klegot/ArdUno_AADsm5-42b/отчет/data/земиля земля.jpg

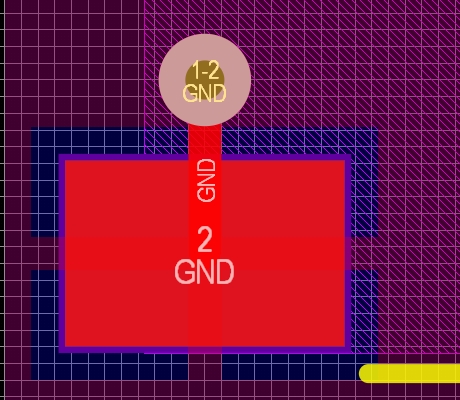
отчет/data/земиля земля.jpg
