klegot/ArdUno_AADsm5-42b/отчет/data/каталог проекта.jpg

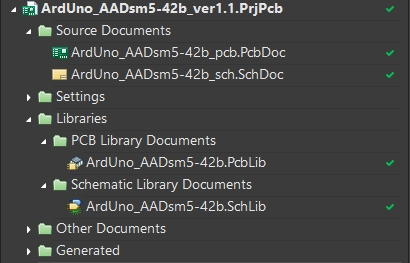
отчет/data/каталог проекта.jpg
