klegot/ArdUno_AADsm5-42b/отчет/data/3D Bottom.PNG

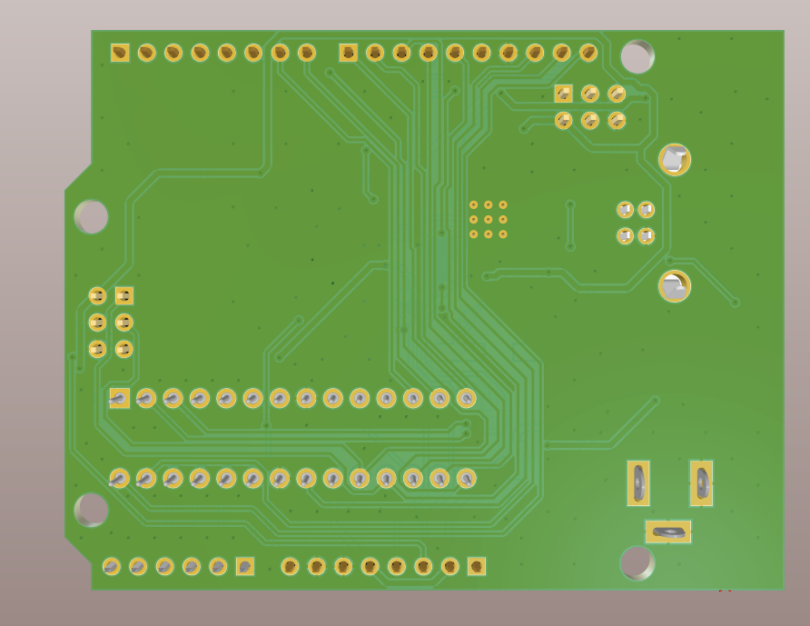
отчет/data/3D Bottom.PNG
