klegot/ArdUno_AADsm5-42b/отчет/data/3D isometric.PNG

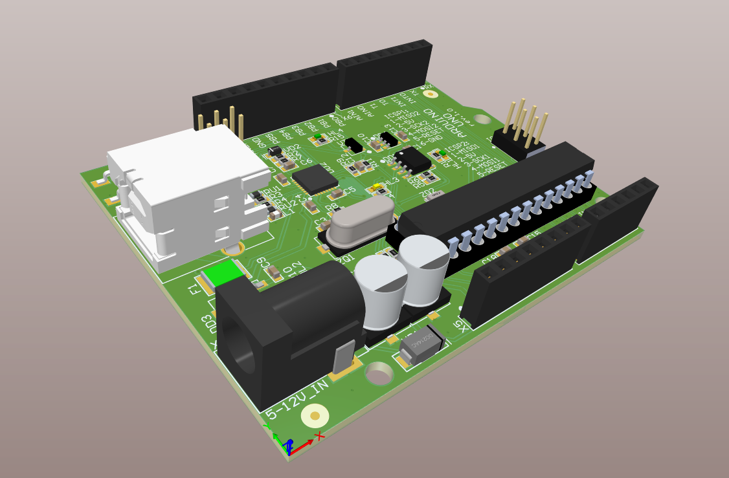
отчет/data/3D isometric.PNG
