klegot/ArdUno_AADsm5-42b/отчет/data/3D Top.PNG

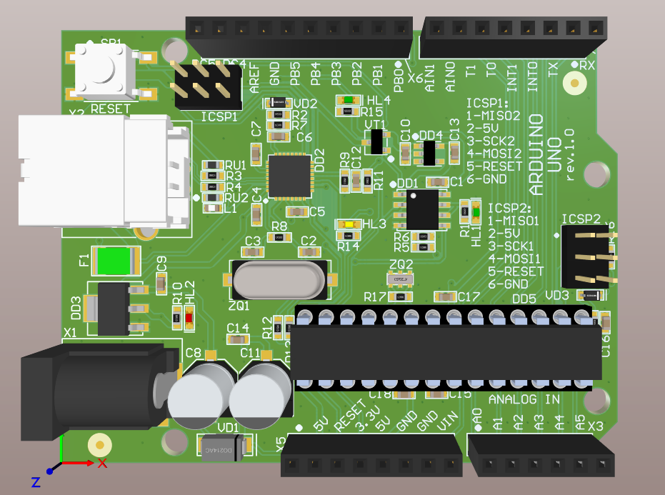
отчет/data/3D Top.PNG
