klegot/ArdUno_AADsm5-42b/отчет/data/atmega 3д.jpg

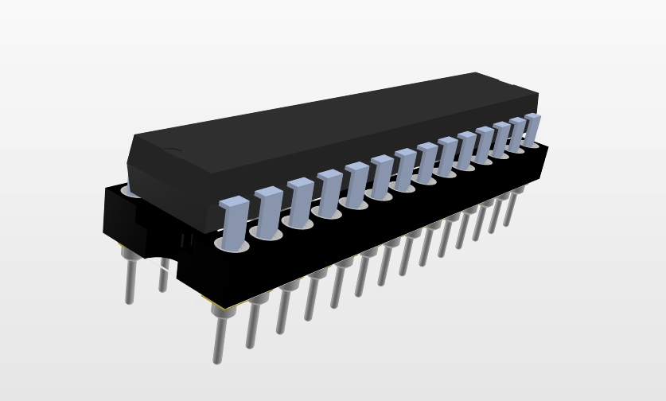
отчет/data/atmega 3д.jpg
