klegot/ArdUno_AADsm5-42b/отчет/data/atmega птм.jpg

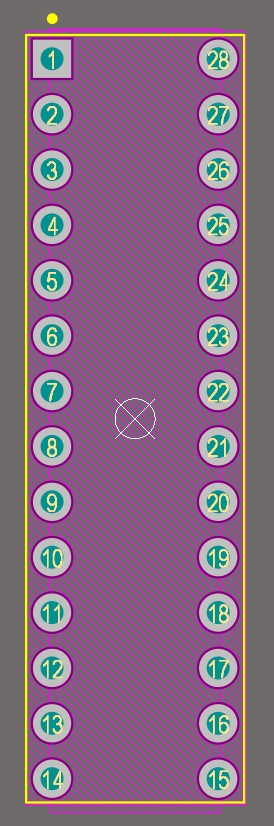
отчет/data/atmega птм.jpg
