klegot/ArdUno_AADsm5-42b/отчет/data/atmega уго + птм.jpg

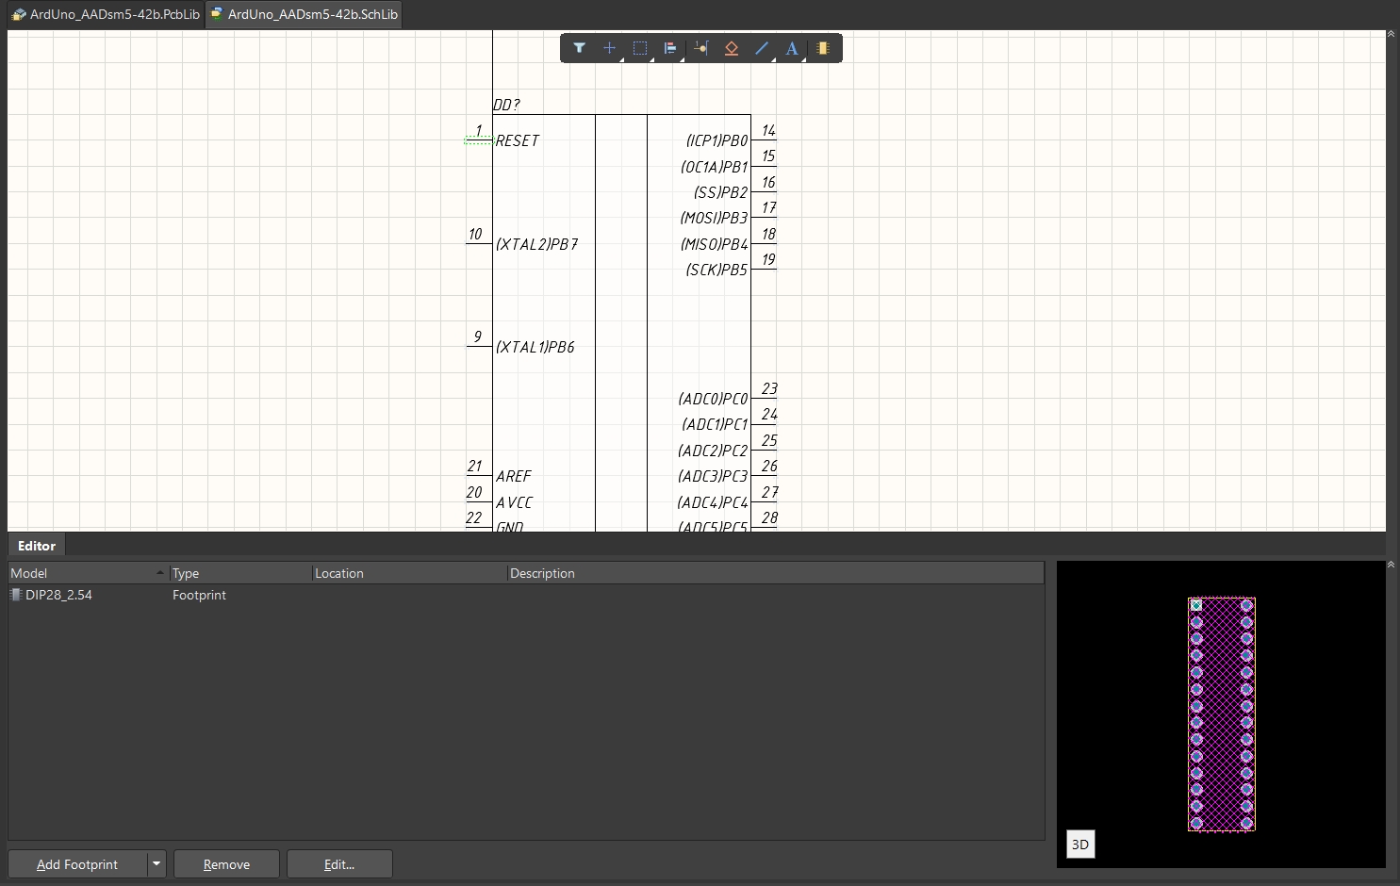
отчет/data/atmega уго + птм.jpg
