klegot/ArdUno_AADsm5-42b/отчет/data/Bottom Layer GERBER.PNG

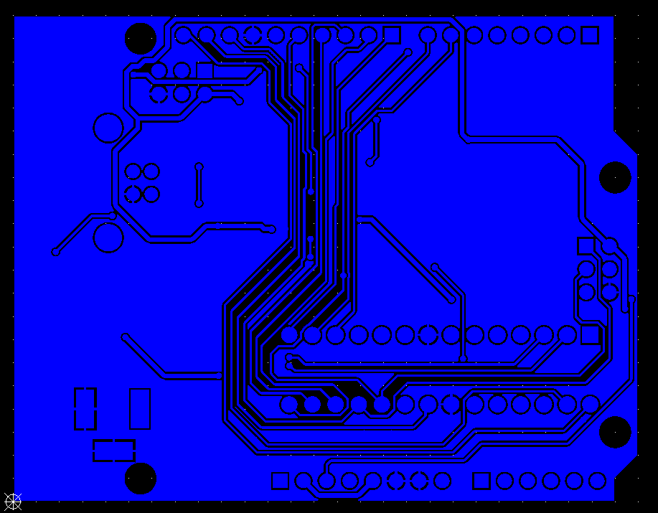
отчет/data/Bottom Layer GERBER.PNG
