klegot/ArdUno_AADsm5-42b/отчет/data/Bottom Layer.PNG

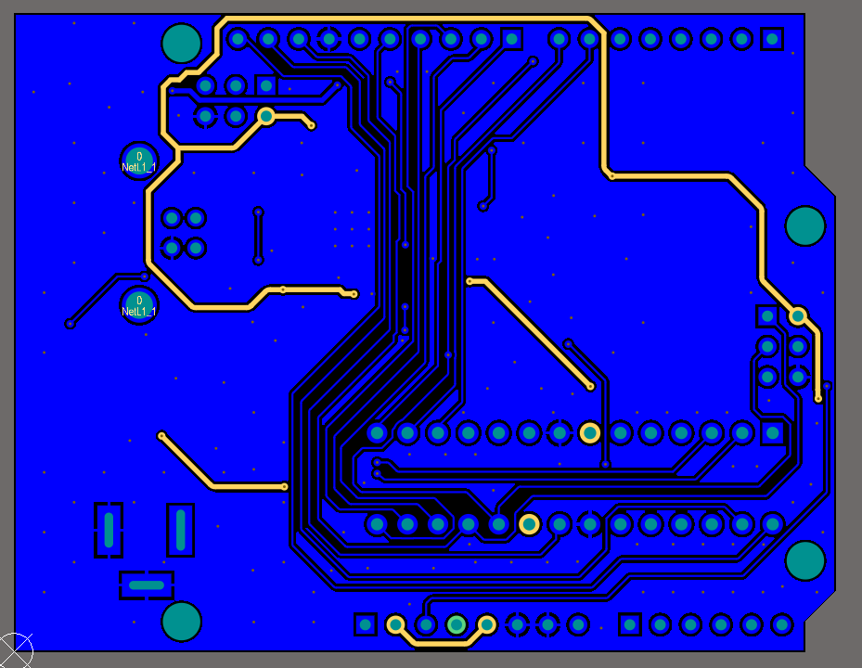
отчет/data/Bottom Layer.PNG
