klegot/ArdUno_AADsm5-42b/отчет/data/Keep Out Layer GERBER.PNG

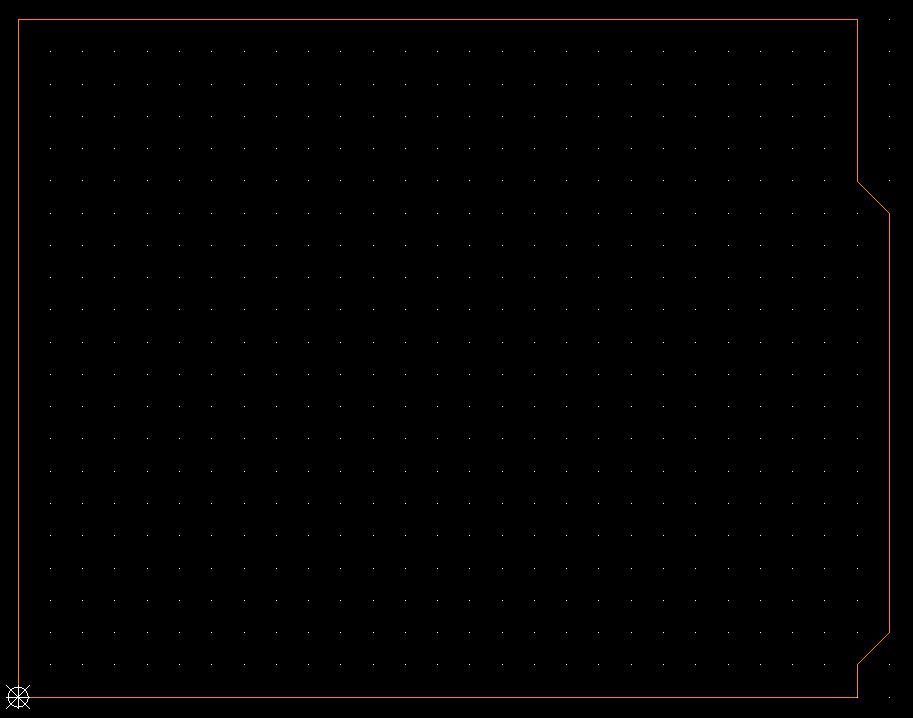
отчет/data/Keep Out Layer GERBER.PNG
