klegot/ArdUno_AADsm5-42b/отчет/data/Overlay GERBER.PNG

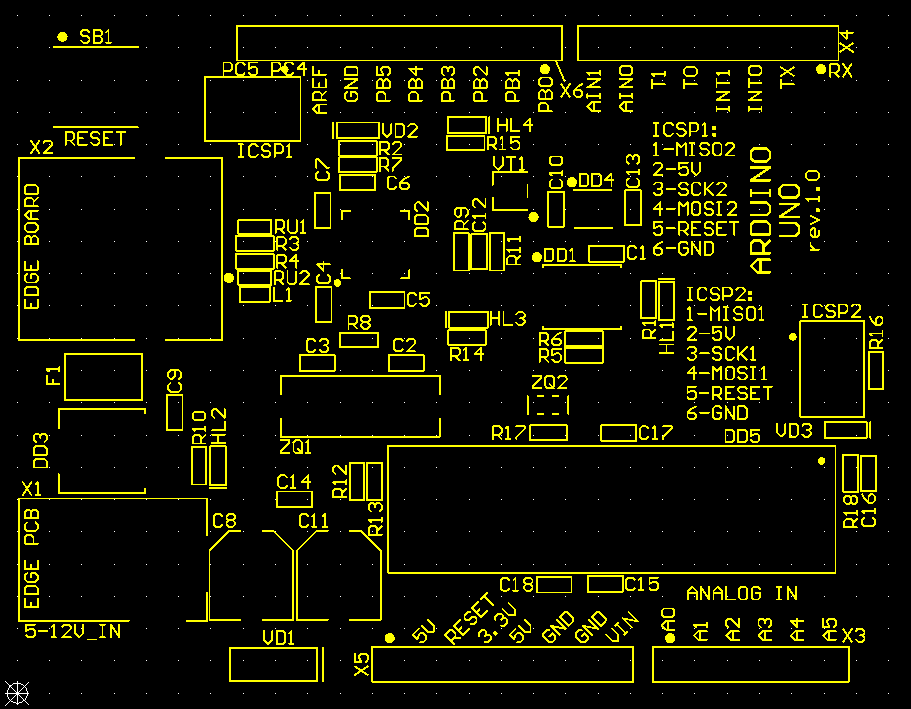
отчет/data/Overlay GERBER.PNG
