klegot/ArdUno_AADsm5-42b/отчет/data/Top Layer GERBER.PNG

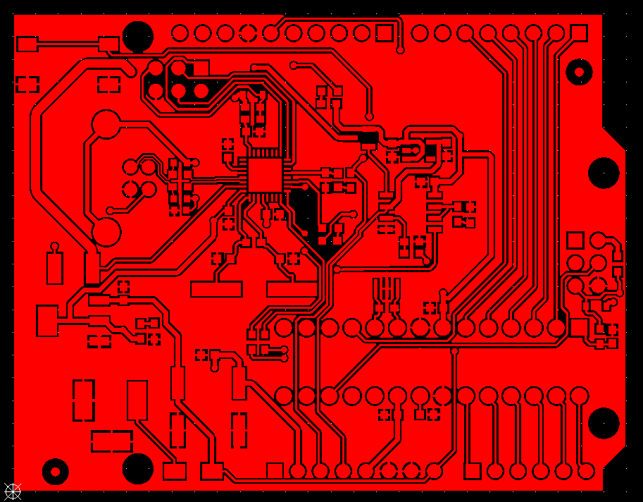
отчет/data/Top Layer GERBER.PNG
