klegot/ArdUno_AADsm5-42b/отчет/data/Top Layer.PNG

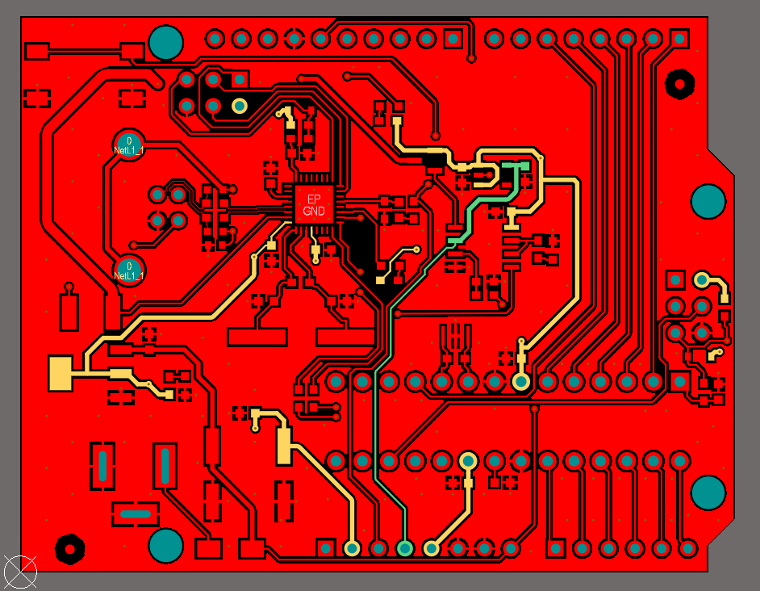
отчет/data/Top Layer.PNG
