klegot/ArdUno_AADsm5-42b/отчет/data/Top Overlay.PNG

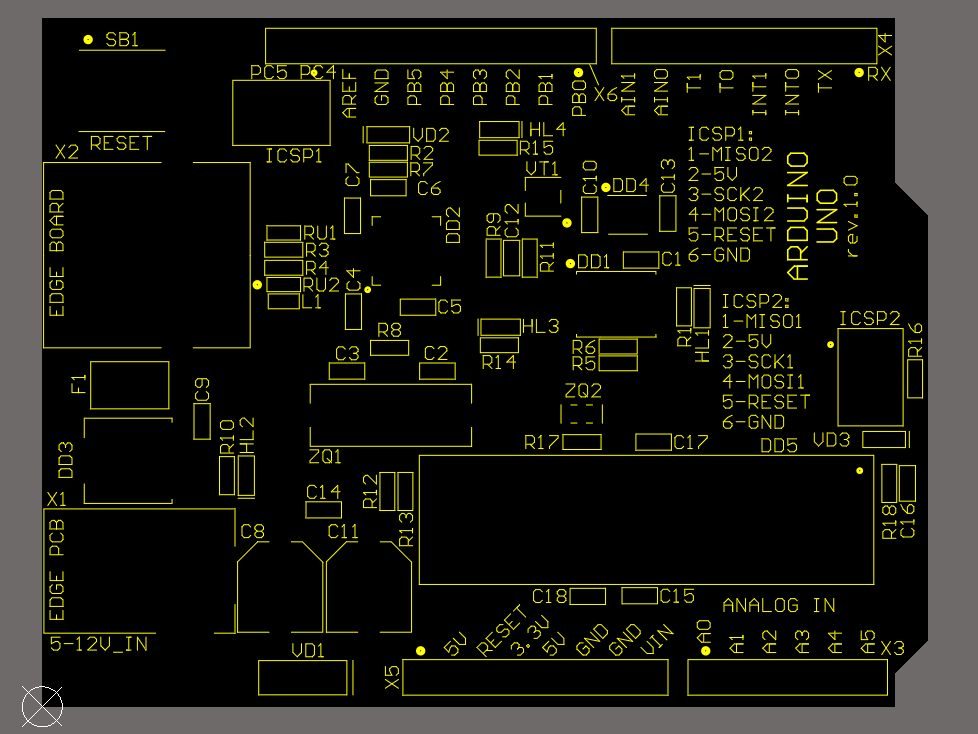
отчет/data/Top Overlay.PNG
