klegot/ArdUno_AADsm5-42b/отчет/data/капаситор 3д.jpg

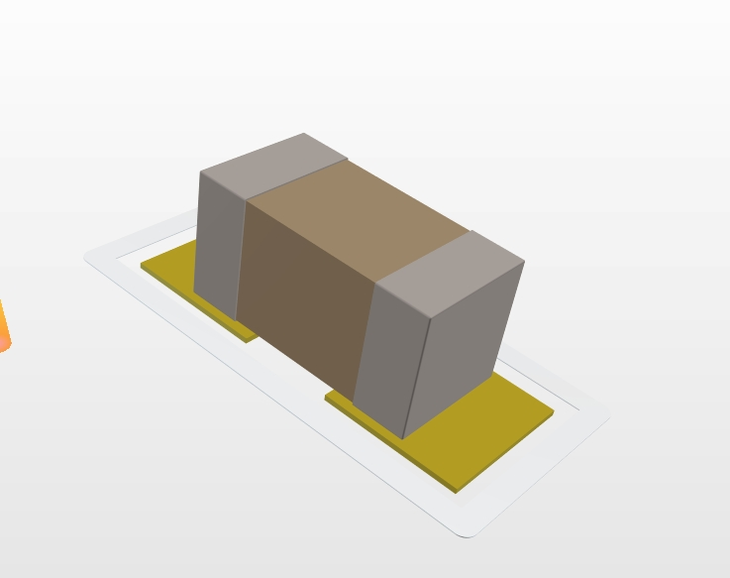
отчет/data/капаситор 3д.jpg
