klegot/ArdUno_AADsm5-42b/отчет/data/капаситор уо +птм.jpg

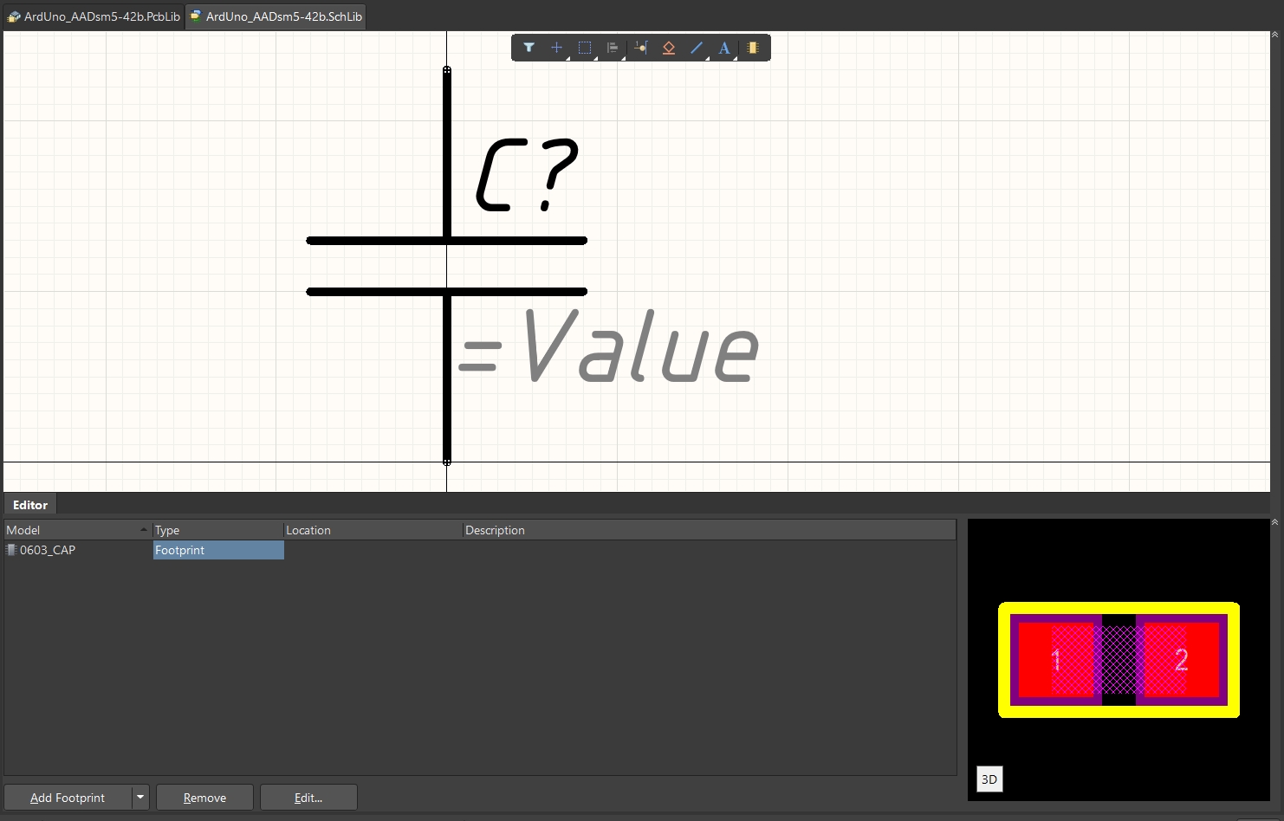
отчет/data/капаситор уо +птм.jpg
