klegot/ArdUno_AADsm5-42b/отчет/data/Сверловка.PNG

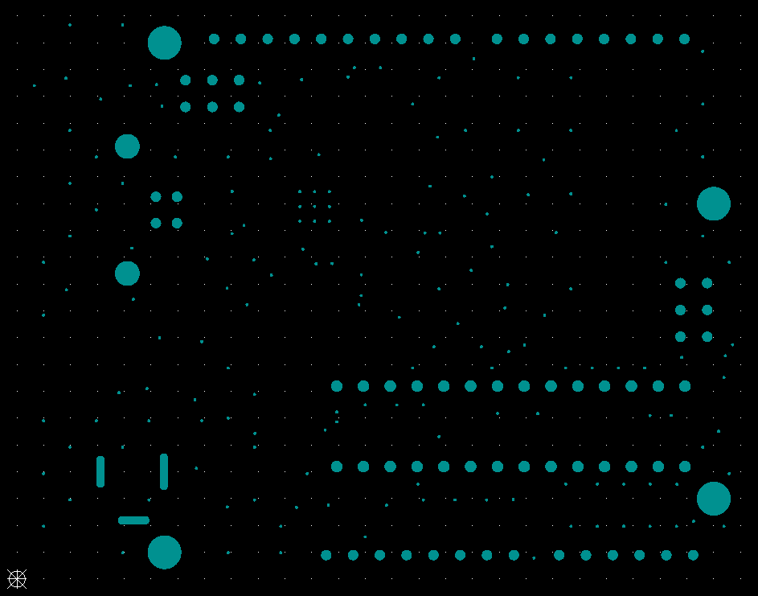
отчет/data/Сверловка.PNG
