klegot/ArdUno_AADsm5-42b/отчет/data/Bottom Solder GERBER.PNG

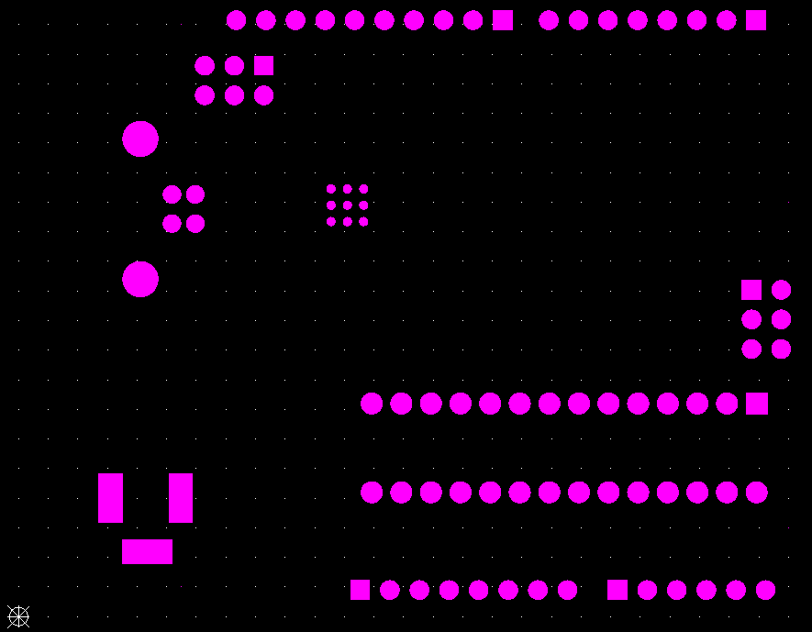
отчет/data/Bottom Solder GERBER.PNG
