klegot/ArdUno_AADsm5-42b/отчет/data/Bottom Solder.PNG

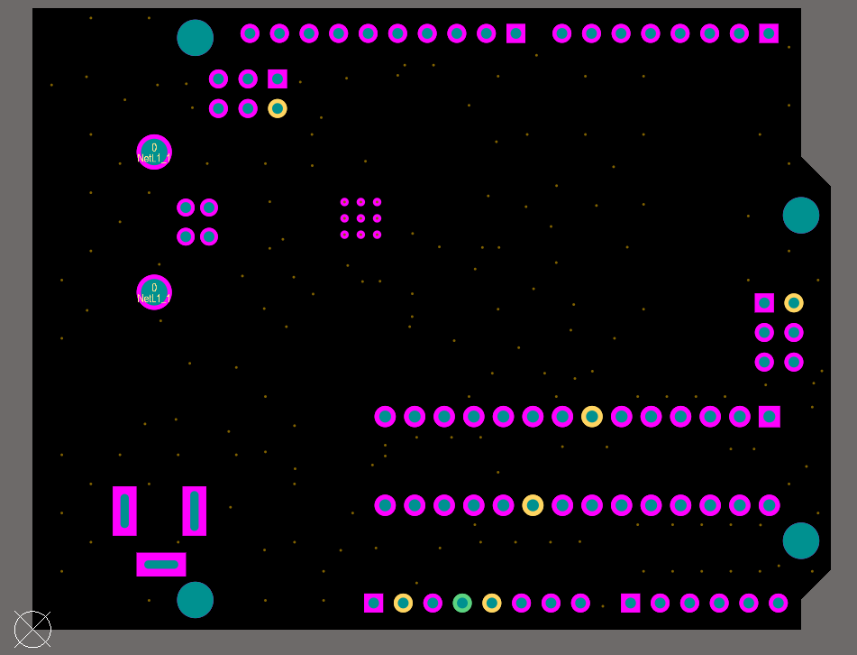
отчет/data/Bottom Solder.PNG
