klegot/ArdUno_AADsm5-42b/отчет/data/Top Solder GERBER.PNG

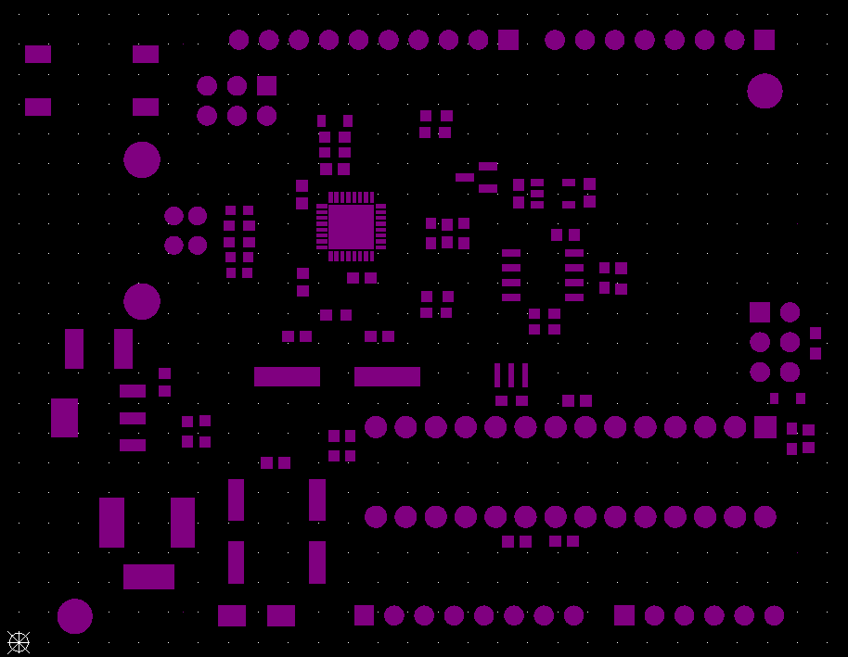
отчет/data/Top Solder GERBER.PNG
