klegot/ArdUno_AADsm5-42b/отчет/data/Top Solder.PNG

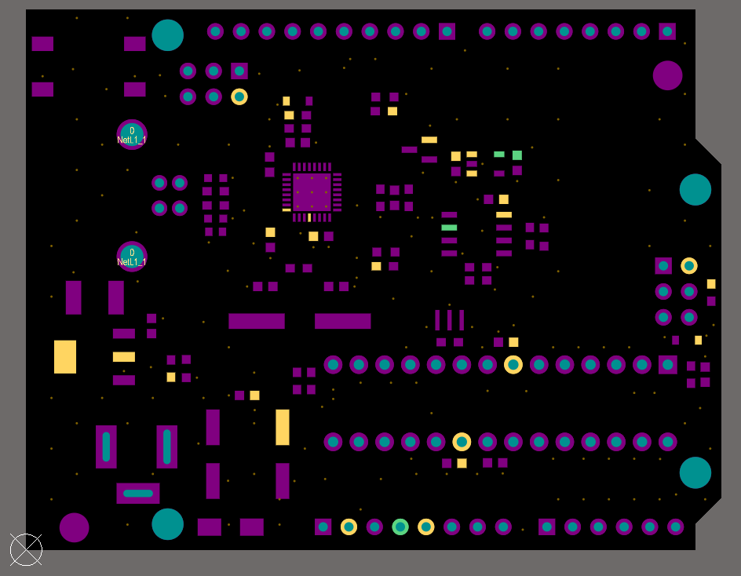
отчет/data/Top Solder.PNG
